sensint/haptic-things/Pictures/DSCF5339.JPG

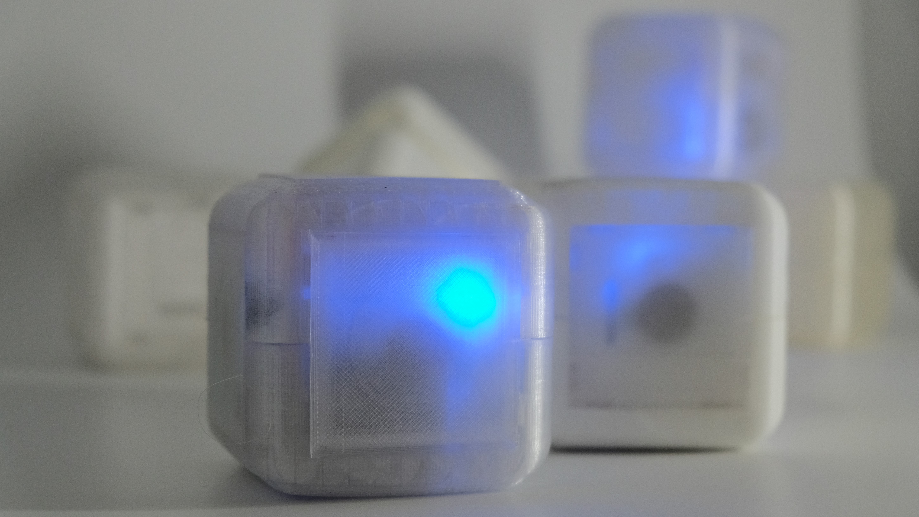
Pictures/DSCF5339.JPG
