sensint/haptic-things/Pictures/DSCF5357.JPG

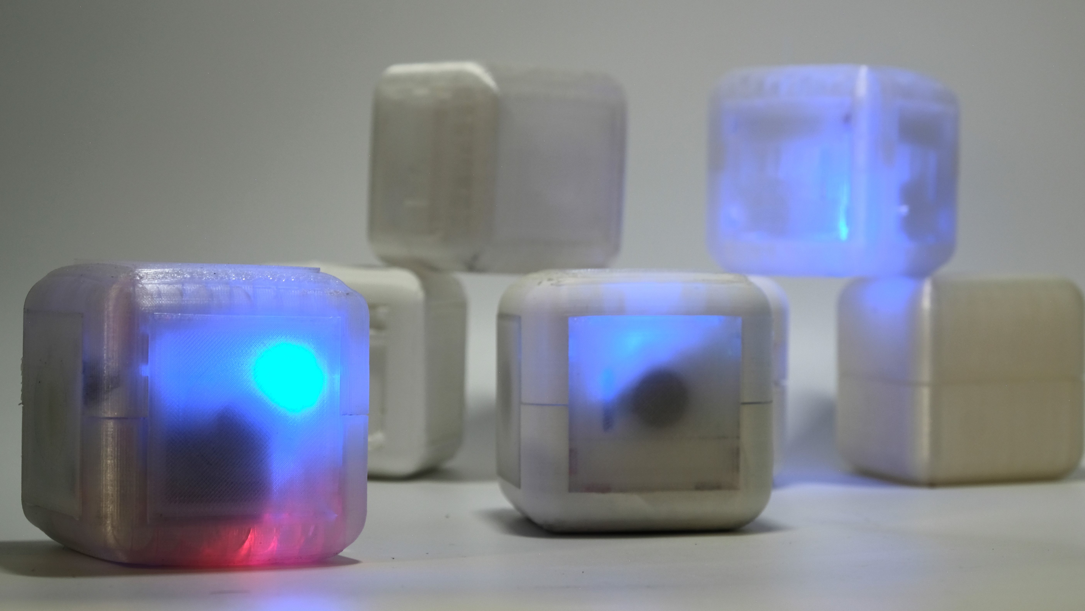
Pictures/DSCF5357.JPG
